California-Strawberry-Commission/oas-data-logger/software/dlflib/src/fnv.c

/*
 * fnv - Fowler/Noll/Vo- hash code
 *
 * The basis of this hash algorithm was taken from an idea sent
 * as reviewer comments to the IEEE POSIX P1003.2 committee by:
 *
 *      Phong Vo (http://www.research.att.com/info/kpv/)
 *      Glenn Fowler (http://www.research.att.com/~gsf/)
 *
 * In a subsequent ballot round:
 *
 *      Landon Curt Noll (http://www.isthe.com/chongo/)
 *
 * improved on their algorithm.  Some people tried this hash
 * and found that it worked rather well.  In an EMail message
 * to Landon, they named it the ``Fowler/Noll/Vo'' or FNV hash.
 *
 * FNV hashes are designed to be fast while maintaining a low
 * collision rate. The FNV speed allows one to quickly hash lots
 * of data while maintaining a reasonable collision rate.  See:
 *
 *      http://www.isthe.com/chongo/tech/comp/fnv/index.html
 *
 * for more details as well as other forms of the FNV hash.
 *
 ***
 *
 * To use the recommended 32 bit FNV-1 hash, pass FNV1_32_INIT as the
 * Fnv32_t hashval argument to fnv_32_buf() or fnv_32_str().
 *
 * To use the recommended 64 bit FNV-1 hash, pass FNV1_64_INIT as the
 * Fnv64_t hashval argument to fnv_64_buf() or fnv_64_str().
 *
 * To use the recommended 32 bit FNV-1a hash, pass FNV1_32A_INIT as the
 * Fnv32_t hashval argument to fnv_32a_buf() or fnv_32a_str().
 *
 * To use the recommended 64 bit FNV-1a hash, pass FNV1A_64_INIT as the
 * Fnv64_t hashval argument to fnv_64a_buf() or fnv_64a_str().
 *
 ***
 *
 * Please do not copyright this code.  This code is in the public domain.
 *
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
 * By:
 *	chongo <Landon Curt Noll> /\oo/\
 *      http://www.isthe.com/chongo/
 *
 * Share and Enjoy!	:-)
 */

#include <fnv.h>
#include <stdlib.h>

/*
 * 32 bit magic FNV-0 and FNV-1 prime
 */
#define FNV_32_PRIME ((Fnv32_t)0x01000193)

/*
 * fnv_32_buf - perform a 32 bit Fowler/Noll/Vo hash on a buffer
 *
 * input:
 *	buf	- start of buffer to hash
 *	len	- length of buffer in octets
 *	hval	- previous hash value or 0 if first call
 *
 * returns:
 *	32 bit hash as a static hash type
 *
 * NOTE: To use the 32 bit FNV-0 historic hash, use FNV0_32_INIT as the hval
 *	 argument on the first call to either fnv_32_buf() or fnv_32_str().
 *
 * NOTE: To use the recommended 32 bit FNV-1 hash, use FNV1_32_INIT as the hval
 *	 argument on the first call to either fnv_32_buf() or fnv_32_str().
 */
Fnv32_t fnv_32_buf(const void *buf, size_t len, Fnv32_t hval) {
  unsigned char *bp = (unsigned char *)buf; /* start of buffer */
  unsigned char *be = bp + len;             /* beyond end of buffer */

  /*
   * FNV-1 hash each octet in the buffer
   */
  while (bp < be) {
    /* multiply by the 32 bit FNV magic prime mod 2^32 */
#if defined(NO_FNV_GCC_OPTIMIZATION)
    hval *= FNV_32_PRIME;
#else
    hval +=
        (hval << 1) + (hval << 4) + (hval << 7) + (hval << 8) + (hval << 24);
#endif

    /* xor the bottom with the current octet */
    hval ^= (Fnv32_t)*bp++;
  }

  /* return our new hash value */
  return hval;
}

/*
 * fnv_32_str - perform a 32 bit Fowler/Noll/Vo hash on a string
 *
 * input:
 *	str	- string to hash
 *	hval	- previous hash value or 0 if first call
 *
 * returns:
 *	32 bit hash as a static hash type
 *
 * NOTE: To use the 32 bit FNV-0 historic hash, use FNV0_32_INIT as the hval
 *	 argument on the first call to either fnv_32_buf() or fnv_32_str().
 *
 * NOTE: To use the recommended 32 bit FNV-1 hash, use FNV1_32_INIT as the hval
 *	 argument on the first call to either fnv_32_buf() or fnv_32_str().
 */
Fnv32_t fnv_32_str(char *str, Fnv32_t hval) {
  unsigned char *s = (unsigned char *)str; /* unsigned string */

  /*
   * FNV-1 hash each octet in the buffer
   */
  while (*s) {
    /* multiply by the 32 bit FNV magic prime mod 2^32 */
#if defined(NO_FNV_GCC_OPTIMIZATION)
    hval *= FNV_32_PRIME;
#else
    hval +=
        (hval << 1) + (hval << 4) + (hval << 7) + (hval << 8) + (hval << 24);
#endif

    /* xor the bottom with the current octet */
    hval ^= (Fnv32_t)*s++;
  }

  /* return our new hash value */
  return hval;
}

/*
 * fnv_32a_buf - perform a 32 bit Fowler/Noll/Vo FNV-1a hash on a buffer
 *
 * input:
 *	buf	- start of buffer to hash
 *	len	- length of buffer in octets
 *	hval	- previous hash value or 0 if first call
 *
 * returns:
 *	32 bit hash as a static hash type
 *
 * NOTE: To use the recommended 32 bit FNV-1a hash, use FNV1_32A_INIT as the
 * 	 hval arg on the first call to either fnv_32a_buf() or fnv_32a_str().
 */
Fnv32_t fnv_32a_buf(void *buf, size_t len, Fnv32_t hval) {
  unsigned char *bp = (unsigned char *)buf; /* start of buffer */
  unsigned char *be = bp + len;             /* beyond end of buffer */

  /*
   * FNV-1a hash each octet in the buffer
   */
  while (bp < be) {
    /* xor the bottom with the current octet */
    hval ^= (Fnv32_t)*bp++;

    /* multiply by the 32 bit FNV magic prime mod 2^32 */
#if defined(NO_FNV_GCC_OPTIMIZATION)
    hval *= FNV_32_PRIME;
#else
    hval +=
        (hval << 1) + (hval << 4) + (hval << 7) + (hval << 8) + (hval << 24);
#endif
  }

  /* return our new hash value */
  return hval;
}

/*
 * fnv_32a_str - perform a 32 bit Fowler/Noll/Vo FNV-1a hash on a string
 *
 * input:
 *	str	- string to hash
 *	hval	- previous hash value or 0 if first call
 *
 * returns:
 *	32 bit hash as a static hash type
 *
 * NOTE: To use the recommended 32 bit FNV-1a hash, use FNV1_32A_INIT as the
 *  	 hval arg on the first call to either fnv_32a_buf() or fnv_32a_str().
 */
Fnv32_t fnv_32a_str(char *str, Fnv32_t hval) {
  unsigned char *s = (unsigned char *)str; /* unsigned string */

  /*
   * FNV-1a hash each octet in the buffer
   */
  while (*s) {
    /* xor the bottom with the current octet */
    hval ^= (Fnv32_t)*s++;

    /* multiply by the 32 bit FNV magic prime mod 2^32 */
#if defined(NO_FNV_GCC_OPTIMIZATION)
    hval *= FNV_32_PRIME;
#else
    hval +=
        (hval << 1) + (hval << 4) + (hval << 7) + (hval << 8) + (hval << 24);
#endif
  }

  /* return our new hash value */
  return hval;
}

/*
 * 64 bit magic FNV-0 and FNV-1 prime
 */
#define FNV_64_PRIME ((Fnv64_t)0x100000001b3ULL)

/*
 * fnv_64_buf - perform a 64 bit Fowler/Noll/Vo hash on a buffer
 *
 * input:
 *	buf	- start of buffer to hash
 *	len	- length of buffer in octets
 *	hval	- previous hash value or 0 if first call
 *
 * returns:
 *	64 bit hash as a static hash type
 *
 * NOTE: To use the 64 bit FNV-0 historic hash, use FNV0_64_INIT as the hval
 *	 argument on the first call to either fnv_64_buf() or fnv_64_str().
 *
 * NOTE: To use the recommended 64 bit FNV-1 hash, use FNV1_64_INIT as the hval
 *	 argument on the first call to either fnv_64_buf() or fnv_64_str().
 */
Fnv64_t fnv_64_buf(void *buf, size_t len, Fnv64_t hval) {
  unsigned char *bp = (unsigned char *)buf; /* start of buffer */
  unsigned char *be = bp + len;             /* beyond end of buffer */

  /*
   * FNV-1 hash each octet of the buffer
   */
  while (bp < be) {
    /* multiply by the 64 bit FNV magic prime mod 2^64 */
#if defined(NO_FNV_GCC_OPTIMIZATION)
    hval *= FNV_64_PRIME;
#else  /* NO_FNV_GCC_OPTIMIZATION */
    hval += (hval << 1) + (hval << 4) + (hval << 5) + (hval << 7) +
            (hval << 8) + (hval << 40);
#endif /* NO_FNV_GCC_OPTIMIZATION */

    /* xor the bottom with the current octet */
    hval ^= (Fnv64_t)*bp++;
  }

  /* return our new hash value */
  return hval;
}

/*
 * fnv_64_str - perform a 64 bit Fowler/Noll/Vo hash on a buffer
 *
 * input:
 *	buf	- start of buffer to hash
 *	hval	- previous hash value or 0 if first call
 *
 * returns:
 *	64 bit hash as a static hash type
 *
 * NOTE: To use the 64 bit FNV-0 historic hash, use FNV0_64_INIT as the hval
 *	 argument on the first call to either fnv_64_buf() or fnv_64_str().
 *
 * NOTE: To use the recommended 64 bit FNV-1 hash, use FNV1_64_INIT as the hval
 *	 argument on the first call to either fnv_64_buf() or fnv_64_str().
 */
Fnv64_t fnv_64_str(char *str, Fnv64_t hval) {
  unsigned char *s = (unsigned char *)str; /* unsigned string */

  /*
   * FNV-1 hash each octet of the string
   */
  while (*s) {
    /* multiply by the 64 bit FNV magic prime mod 2^64 */
#if defined(NO_FNV_GCC_OPTIMIZATION)
    hval *= FNV_64_PRIME;
#else  /* NO_FNV_GCC_OPTIMIZATION */
    hval += (hval << 1) + (hval << 4) + (hval << 5) + (hval << 7) +
            (hval << 8) + (hval << 40);
#endif /* NO_FNV_GCC_OPTIMIZATION */

    /* xor the bottom with the current octet */
    hval ^= (Fnv64_t)*s++;
  }

  /* return our new hash value */
  return hval;
}

/*
 * fnv_64a_buf - perform a 64 bit Fowler/Noll/Vo FNV-1a hash on a buffer
 *
 * input:
 *	buf	- start of buffer to hash
 *	len	- length of buffer in octets
 *	hval	- previous hash value or 0 if first call
 *
 * returns:
 *	64 bit hash as a static hash type
 *
 * NOTE: To use the recommended 64 bit FNV-1a hash, use FNV1A_64_INIT as the
 * 	 hval arg on the first call to either fnv_64a_buf() or fnv_64a_str().
 */
Fnv64_t fnv_64a_buf(void *buf, size_t len, Fnv64_t hval) {
  unsigned char *bp = (unsigned char *)buf; /* start of buffer */
  unsigned char *be = bp + len;             /* beyond end of buffer */

  /*
   * FNV-1a hash each octet of the buffer
   */
  while (bp < be) {
    /* xor the bottom with the current octet */
    hval ^= (Fnv64_t)*bp++;

    /* multiply by the 64 bit FNV magic prime mod 2^64 */
#if defined(NO_FNV_GCC_OPTIMIZATION)
    hval *= FNV_64_PRIME;
#else  /* NO_FNV_GCC_OPTIMIZATION */
    hval += (hval << 1) + (hval << 4) + (hval << 5) + (hval << 7) +
            (hval << 8) + (hval << 40);
#endif /* NO_FNV_GCC_OPTIMIZATION */
  }

  /* return our new hash value */
  return hval;
}

/*
 * fnv_64a_str - perform a 64 bit Fowler/Noll/Vo FNV-1a hash on a buffer
 *
 * input:
 *	buf	- start of buffer to hash
 *	hval	- previous hash value or 0 if first call
 *
 * returns:
 *	64 bit hash as a static hash type
 *
 * NOTE: To use the recommended 64 bit FNV-1a hash, use FNV1A_64_INIT as the
 * 	 hval arg on the first call to either fnv_64a_buf() or fnv_64a_str().
 */
Fnv64_t fnv_64a_str(char *str, Fnv64_t hval) {
  unsigned char *s = (unsigned char *)str; /* unsigned string */

  /*
   * FNV-1a hash each octet of the string
   */
  while (*s) {
    /* xor the bottom with the current octet */
    hval ^= (Fnv64_t)*s++;

    /* multiply by the 64 bit FNV magic prime mod 2^64 */
#if defined(NO_FNV_GCC_OPTIMIZATION)
    hval *= FNV_64_PRIME;
#else  /* NO_FNV_GCC_OPTIMIZATION */
    hval += (hval << 1) + (hval << 4) + (hval << 5) + (hval << 7) +
            (hval << 8) + (hval << 40);
#endif /* NO_FNV_GCC_OPTIMIZATION */
  }

  /* return our new hash value */
  return hval;
}
