California-Strawberry-Commission/oas-data-logger/software/dlflib/src/dlf_logfile.cpp

#include "dlf_logfile.hpp"

#include "datastream/EventStream.hpp"
#include "datastream/PolledStream.hpp"
#include "dlf_cfg.h"
#include "dlf_util.h"
#include "uuid.h"

using std::chrono::microseconds;

namespace dlf {
/**
 * @brief Task responsible for writing data to SD
 * Constantly receives data from _stream streambuffer and writes to SD.
 * @param arg
 */
void LogFile::task_flusher(void *arg) {
  auto self = static_cast<LogFile *>(arg);

  uint8_t buf[DLF_SD_BLOCK_WRITE_SIZE];

  while (self->_state == LOGGING) {
    size_t received = xStreamBufferReceive(self->_stream, buf, sizeof(buf),
                                           pdMS_TO_TICKS(1000));
    self->_f.write(buf, received);
    self->_f.flush();
  }

  /* BEGIN EXIT - NO LONGER IN LOGGING STATE */

  // If errored, exit immediately
  if (self->_state != FLUSHING) {
    Serial.printf("FLUSHER ERROR WITH %x\n", self->_state);

    vTaskDelete(NULL);
    return;
  }

  Serial.println("Flushing remaining bytes...");
  // Flush remaining bytes
  while (xStreamBufferBytesAvailable(self->_stream) > 0 &&
         self->_state == FLUSHING) {
    size_t received = xStreamBufferReceive(self->_stream, buf, sizeof(buf), 0);
    self->_f.write(buf, received);
  }

  self->_state == FLUSHED;
  xSemaphoreGive(self->_sync);

  Serial.printf("Flusher exited cleanly w/ HWM %u\n",
                uxTaskGetStackHighWaterMark(NULL));
  vTaskDelete(NULL);
}

void LogFile::_write_header(dlf_stream_type_e stream_type) {
  dlf_logfile_header_t h;
  h.stream_type = stream_type;
  h.num_streams = _handles.size();
  xStreamBufferSend(_stream, &h, sizeof(h), portMAX_DELAY);

  for (auto &handle : _handles) {
    handle->encode_header_into(_stream);
  }
}

void LogFile::_close_file() {
  // Update header with # of ticks
  _f.seek(offsetof(dlf_logfile_header_t, tick_span));
  _f.write(reinterpret_cast<uint8_t *>(&_last_tick), sizeof(dlf_tick_t));
  Serial.println("calling close");
  _f.close();
}

LogFile::LogFile(stream_handles_t handles, dlf_stream_type_e stream_type,
                 String dir, FS &fs)
    : _fs(fs), _handles(std::move(handles)) {
  _filename = dir + "/" + stream_type_to_string(stream_type) + ".dlf";

  // Set up class internals
  _stream =
      xStreamBufferCreate(DLF_LOGFILE_BUFFER_SIZE, DLF_SD_BLOCK_WRITE_SIZE);
  if (_stream == NULL) {
    _state = STREAM_CREATE_ERROR;
    return;
  }

  _sync = xSemaphoreCreateCounting(1, 0);
  if (_sync == NULL) {
    _state = SYNC_CREATE_ERROR;
    return;
  }

  // Open logfile
  _f = _fs.open(_filename, "w", true);

  if (!_f) {
    _state = FILE_OPEN_ERROR;
    return;
  }

  // Init data flusher
  _state = LOGGING;

  if (xTaskCreate(task_flusher, "Flusher", 2048, this, 5, NULL) != pdTRUE) {
    _state = FLUSHER_CREATE_ERROR;
    return;
  }

  // Initialize logfile
  _write_header(stream_type);
}

/**
 * @brief Samples data. Intended to be externally called at the tick interval.
 *
 * Called by the Run class to trigger a sample.
 *
 * @param tick
 */
void LogFile::sample(dlf_tick_t tick) {
  if (_state != LOGGING) return;

  _last_tick = tick;

  // Sample all handles
  for (auto &h : _handles) {
    if (h->available(tick)) {
      h->encode_into(_stream, tick);
      if (xStreamBufferIsFull(_stream)) _state = QUEUE_FULL;
    }
  }
}

void LogFile::flush() {
    if (_state != LOGGING) return;

    // Wait for the stream buffer to be mostly empty
    // This isn't a perfect guarantee but prevents flushing a file
    // that the flusher task is actively writing to in large chunks.
    while (xStreamBufferBytesAvailable(_stream) > DLF_SD_BLOCK_WRITE_SIZE) {
        vTaskDelay(pdMS_TO_TICKS(10));
    }

    // Update header with the last known number of ticks
    _f.seek(offsetof(dlf_logfile_header_t, tick_span));
    _f.write(reinterpret_cast<uint8_t*>(&_last_tick), sizeof(dlf_tick_t));
    _f.flush(); // Ensure the header update is written to the SD card

    // Return the file pointer to the end for subsequent writes
    _f.seek(_f.size());
}

void LogFile::close() {
  if (_state != LOGGING) return;

  _state = FLUSHING;
  xSemaphoreTake(_sync, portMAX_DELAY);  // wait for flusher to finish up.
  _state = CLOSED;

  // Cleanup dynamic allocations
  vStreamBufferDelete(_stream);
  vSemaphoreDelete(_sync);

  // Finally, update and close file
  _close_file();
  Serial.println("Logfile closed cleanly");
}
}  // namespace dlf
