California-Strawberry-Commission/oas-data-logger/software/dlflib/src/dlf_logger.h

#pragma once

#include <Arduino.h>

#include <chrono>
#include <vector>

#include "components/uploader_component.h"
#include "datastream/EventStream.hpp"
#include "datastream/PolledStream.hpp"
#include "dlf_logfile.hpp"
#include "dlf_run.h"
#include "dlf_types.h"

#define POLL(type_name)                                                      \
  CSCLogger &poll(type_name &value, String id, microseconds sample_interval, \
                  microseconds phase = microseconds::zero(),                 \
                  const char *notes = nullptr) {                             \
    return _poll(Encodable(value, #type_name), id, sample_interval, phase,   \
                 notes);                                                     \
  }                                                                          \
  inline CSCLogger &poll(type_name &value, String id,                        \
                         microseconds sample_interval, const char *notes) {  \
    return _poll(Encodable(value, #type_name), id, sample_interval,          \
                 microseconds::zero(), notes);                               \
  }

#define WATCH(type_name)                                                       \
  CSCLogger &watch(type_name &value, String id, const char *notes = nullptr) { \
    return _watch(Encodable(value, #type_name), id, notes);                    \
  }

#define INDEX_FILE_PATH "/__INDEX"
#define BLOCK_SIZE 512
#define NUM_BLOCKS 10
#define BLOCK_OVERHEAD 512
#define MAX_RUNS 1

// 0 is error, > 0 is valid handle
typedef int run_handle_t;

class CSCLogger : public DlfComponent {
  typedef std::chrono::microseconds microseconds;
  typedef std::chrono::milliseconds milliseconds;

  std::unique_ptr<dlf::Run> runs[MAX_RUNS];

  // Todo: Figure out how to do this with unique_ptrs
  dlf::datastream::streams_t data_streams;

  FS &_fs;
  String fs_dir;

  std::vector<DlfComponent *> components;

 public:
  enum LoggerEvents : uint32_t { NEW_RUN = 1 };

  EventGroupHandle_t ev;

  CSCLogger(FS &fs, String fs_dir = "/");

  bool begin();

  run_handle_t get_available_handle();

  run_handle_t start_run(Encodable meta,
                         microseconds tick_rate = milliseconds(100));

  void stop_run(run_handle_t h);
  
  void flush(run_handle_t h);

  bool run_is_active(const char *uuid);

  CSCLogger &_watch(Encodable value, String id, const char *notes);
  WATCH(uint8_t)
  WATCH(uint16_t)
  WATCH(uint32_t)
  WATCH(uint64_t)
  WATCH(int8_t)
  WATCH(int16_t)
  WATCH(int32_t)
  WATCH(int64_t)
  WATCH(bool)
  WATCH(double)
  WATCH(float)

  CSCLogger &_poll(Encodable value, String id, microseconds sample_interval,
                   microseconds phase, const char *notes);
  POLL(uint8_t)
  POLL(uint16_t)
  POLL(uint32_t)
  POLL(uint64_t)
  POLL(int8_t)
  POLL(int16_t)
  POLL(int32_t)
  POLL(int64_t)
  POLL(bool)
  POLL(double)
  POLL(float)

  CSCLogger &syncTo(String host, uint16_t port,
                    const UploaderComponent::Options &options);
  void waitForSyncCompletion();

  void prune();
};

#undef POLL
#undef WATCH

#define WATCH(logger, value, ...) logger.watch(value, #value, ##__VA_ARGS__)
#define POLL(logger, value, ...) logger.poll(value, #value, ##__VA_ARGS__)
