California-Strawberry-Commission/oas-data-logger/software/dlflib/src/dlf_logfile.hpp

#pragma once
#include <Arduino.h>
#include <freertos/stream_buffer.h>

#include <vector>

#include <FS.h>
#include "datastream/AbstractStreamHandle.hpp"
#include "dlf_types.h"

namespace dlf
{
    using namespace datastream;
    using namespace std;

    /**
     * @brief Handles logging of datastreams to files.
     *
     * Handles a SINGLE TYPE of datastream handle (IE polled/event).
     * All data sampled by a LogFile class is written into a single contiguous file.
     * Sampled data is written into chunks that are then pushed to the provided queue.
     * The provided queue should write the passed chunks to the specified pointer.
     *
     * LogFiles do NOT create tasks themselves. All RTOS task creation is handled by
     * the Run class (which manages multiple LogFile instances)
     *
     * https://stackoverflow.com/questions/8915873/how-much-work-should-constructor-of-my-class-perform
     */
    class LogFile
    {
    protected:
        /**
         * @brief Data stream handles logged by this logfile
         */
        stream_handles_t _handles;

        FS &_fs;
        String _filename;
        File _f;

        /**
         * @brief Streambuffer responsible for transferring data from sampler task to SD writer task
         */
        StreamBufferHandle_t _stream;
        dlf_file_state_e _state;
        SemaphoreHandle_t _sync;
        dlf_tick_t _last_tick;

        /**
         * @brief Writes a complete header into this logfile.
         *
         * Uses existing streambuffer architecture because why not.
         */
        void _write_header(dlf_stream_type_e stream_type);

        

        /**
         * Updates and closes the underlying file. Does not flush internal
         * buffers
         */
        void _close_file();

        /**
         * @brief Task responsible for writing data to SD
         * Constantly receives data from _stream streambuffer and writes to SD.
         * @param arg
         */
        static void task_flusher(void *arg);

    public:
        LogFile(stream_handles_t handles, dlf_stream_type_e stream_type, String dir, FS &fs);

        /**
         * Samples data. Intended to be externally called at the tick interval.
         * Called by the Run class to trigger a sample.
         */
        void sample(dlf_tick_t tick);

        /**
         * Flushes and closes this logfile
         */
        void close();

        void flush();

    };
} // namespace dlf
