California-Strawberry-Commission/oas-data-logger/software/dlflib/src/components/uploader_component.h

#pragma once

#include <Arduino.h>
#include <FS.h>
#include <WiFi.h>

#include <functional>

#include "dlf_component.h"

class UploaderComponent : public DlfComponent {
 public:
  static void syncTask(void *arg);

  struct Options {
    bool deleteAfterUpload = false;
    bool markAfterUpload = true;
  };
  UploaderComponent(FS &fs, String fsDir, String host, uint16_t port,
                    const Options &options);
  bool begin();
  bool uploadRun(File runDir, String path);
  void waitForSyncCompletion();

 private:
  enum WifiEvent {
    WLAN_READY = 1,
  };
  enum SyncEvent {
    SYNC_COMPLETE = 1,
  };

  // https://github.com/espressif/arduino-esp32/blob/master/libraries/WiFi/examples/WiFiClientEvents/WiFiClientEvents.ino
  void onWifiDisconnected(arduino_event_id_t event, arduino_event_info_t info);
  void onWifiConnected(arduino_event_id_t event, arduino_event_info_t info);

  FS &fs_;
  String dir_;
  String host_;
  uint16_t port_;
  Options options_;
  // Used to notify when WiFi connected/disconnected
  EventGroupHandle_t wifiEvent_;
  // Used to notify when sync is in progress/complete
  EventGroupHandle_t syncEvent_;
};
