California-Strawberry-Commission/oas-data-logger/software/dlflib/src/dlf_util.h

#pragma once

#include <Arduino.h>

// https://stackoverflow.com/questions/3553296/sizeof-single-struct-member-in-c
#define member_sizeof(type, member) sizeof(((type *)0)->member)

// https://stackoverflow.com/a/59522794/16238567
inline constexpr size_t hash_str(const char *s, int off = 0) {
  return !s[off] ? 5381 : (hash_str(s, off + 1) * 33) ^ s[off];
}

inline unsigned int hash(uint8_t *s, size_t len) {
  unsigned int h = 5381;
  for (int i = len - 1; i >= 0; i--) {
    h = h * 33 ^ s[i];
  }
  return h;
}

template <typename T>
inline constexpr const char *t() {
#ifdef _MSC_VER
  return __FUNCSIG__;
#else
  return __PRETTY_FUNCTION__;
#endif
}

/**
 * Generates a characteristic type name for the passed
 * type using GCC's __PRETTY_FUNCTION__
 * This string should be parsable to get the actual type's name.
 */
template <typename T>
inline constexpr const char *characteristic_type_name() {
  return t<T>();
}

template <typename T>
inline constexpr size_t hash_type() {
  return hash_str(t<T>());
}

/**
 * Copies a string to heap-allocated memory, and sets the passed pointer to said
 * memory. If heap memory already exists at str_dest, it is realloced.
 */
inline void str2heap(char **str_dest, const char *str) {
  // Make size always at least 1.
  size_t s = str == nullptr ? 1 : strlen(str) + 1;

  // Set destination to new (or reallocated) memory
  *str_dest = (char *)realloc(*str_dest, s);

  // ensure a null-term in target string
  *str_dest[0] = '\0';

  // Don't copy string if it's null.
  if (str != nullptr) strlcpy(*str_dest, str, s);
}

/**
 * Joins multiple path segments into a normalized path
 */
inline String resolvePath(std::initializer_list<String> parts) {
  String result = "";

  for (const String &part : parts) {
    if (part.length() == 0) continue;

    if (result.endsWith("/") && part.startsWith("/")) {
      result += part.substring(1);
    } else if (!result.endsWith("/") && !part.startsWith("/")) {
      result += "/" + part;
    } else {
      result += part;
    }
  }

  return result.length() == 0 ? "/" : result;
}
